moehambouta/Mixed-Signal-PCB/.pages/assets/pcb_3d.gif

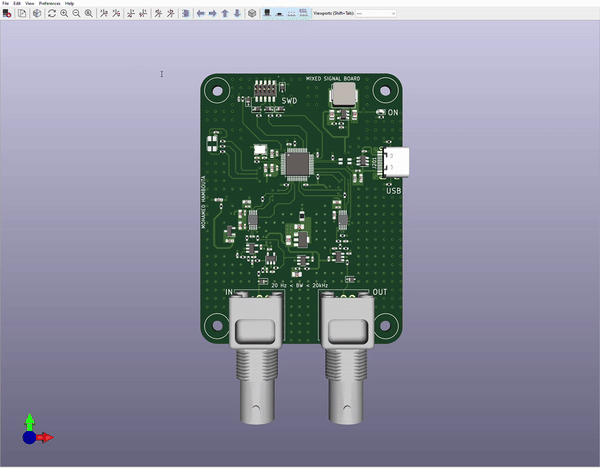
.pages/assets/pcb_3d.gif
