moehambouta/Mixed-Signal-PCB/.pages/assets/adc1.png

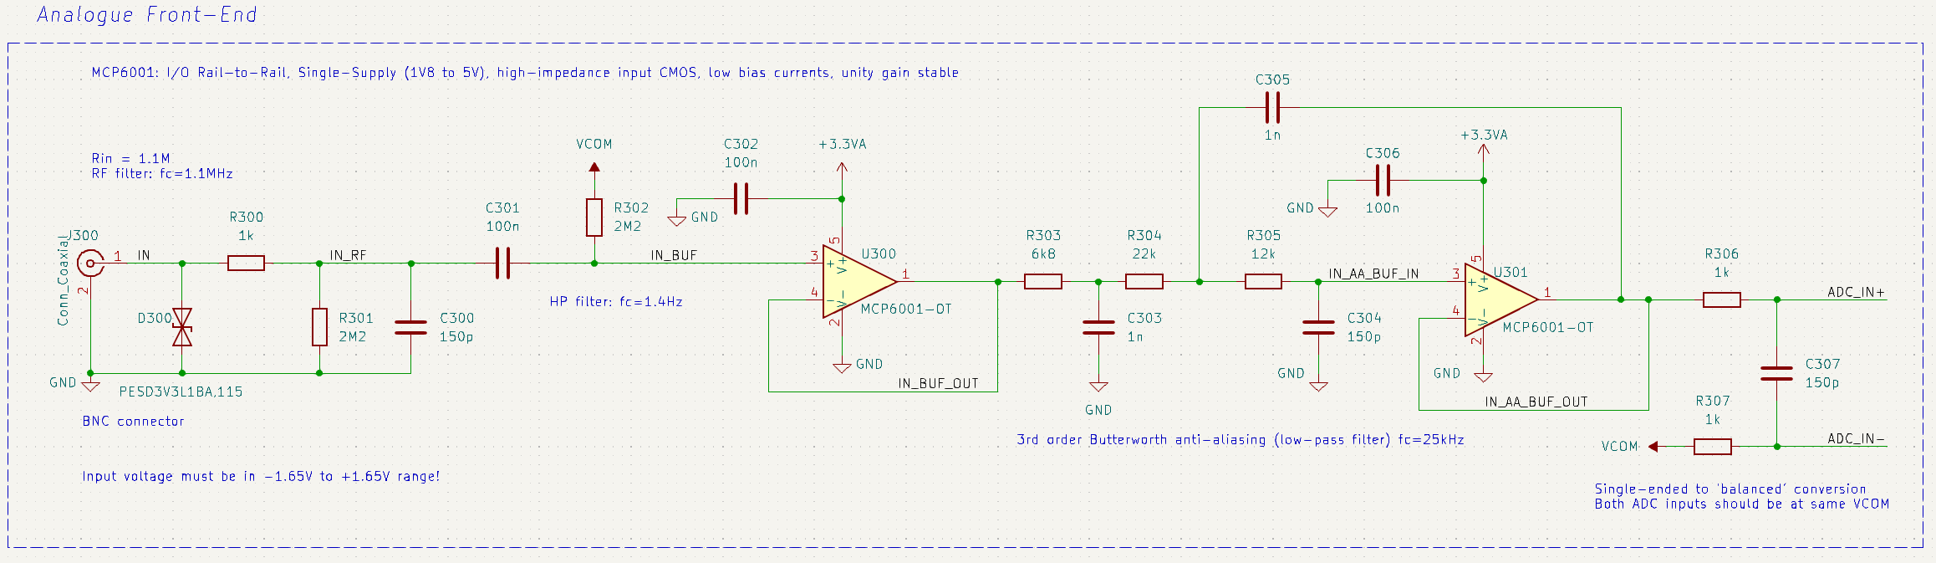
.pages/assets/adc1.png
