moehambouta/Mixed-Signal-PCB/.pages/assets/adc2.png

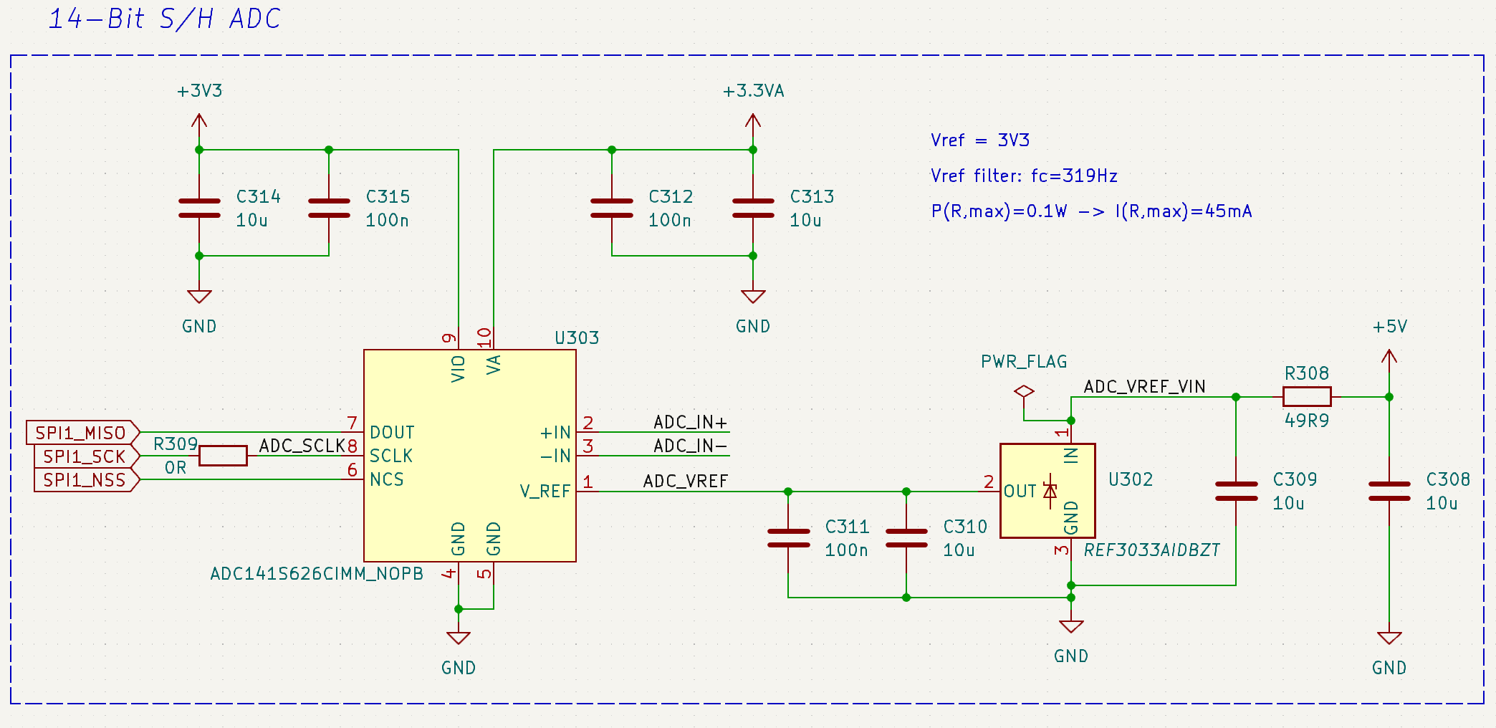
.pages/assets/adc2.png
