moehambouta/Mixed-Signal-PCB/.pages/assets/dac.png

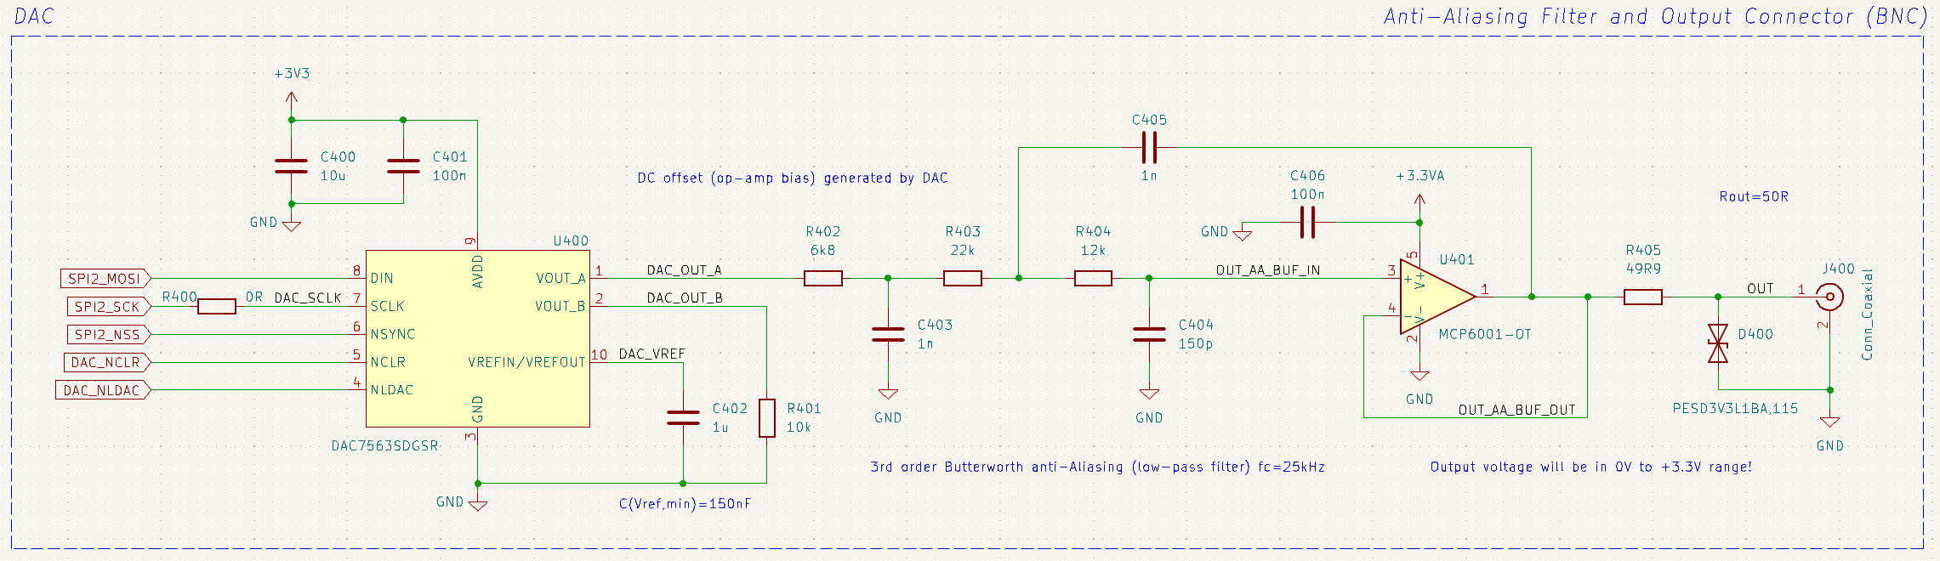
.pages/assets/dac.png
