moehambouta/Mixed-Signal-PCB/.pages/assets/pcb_bcu.png

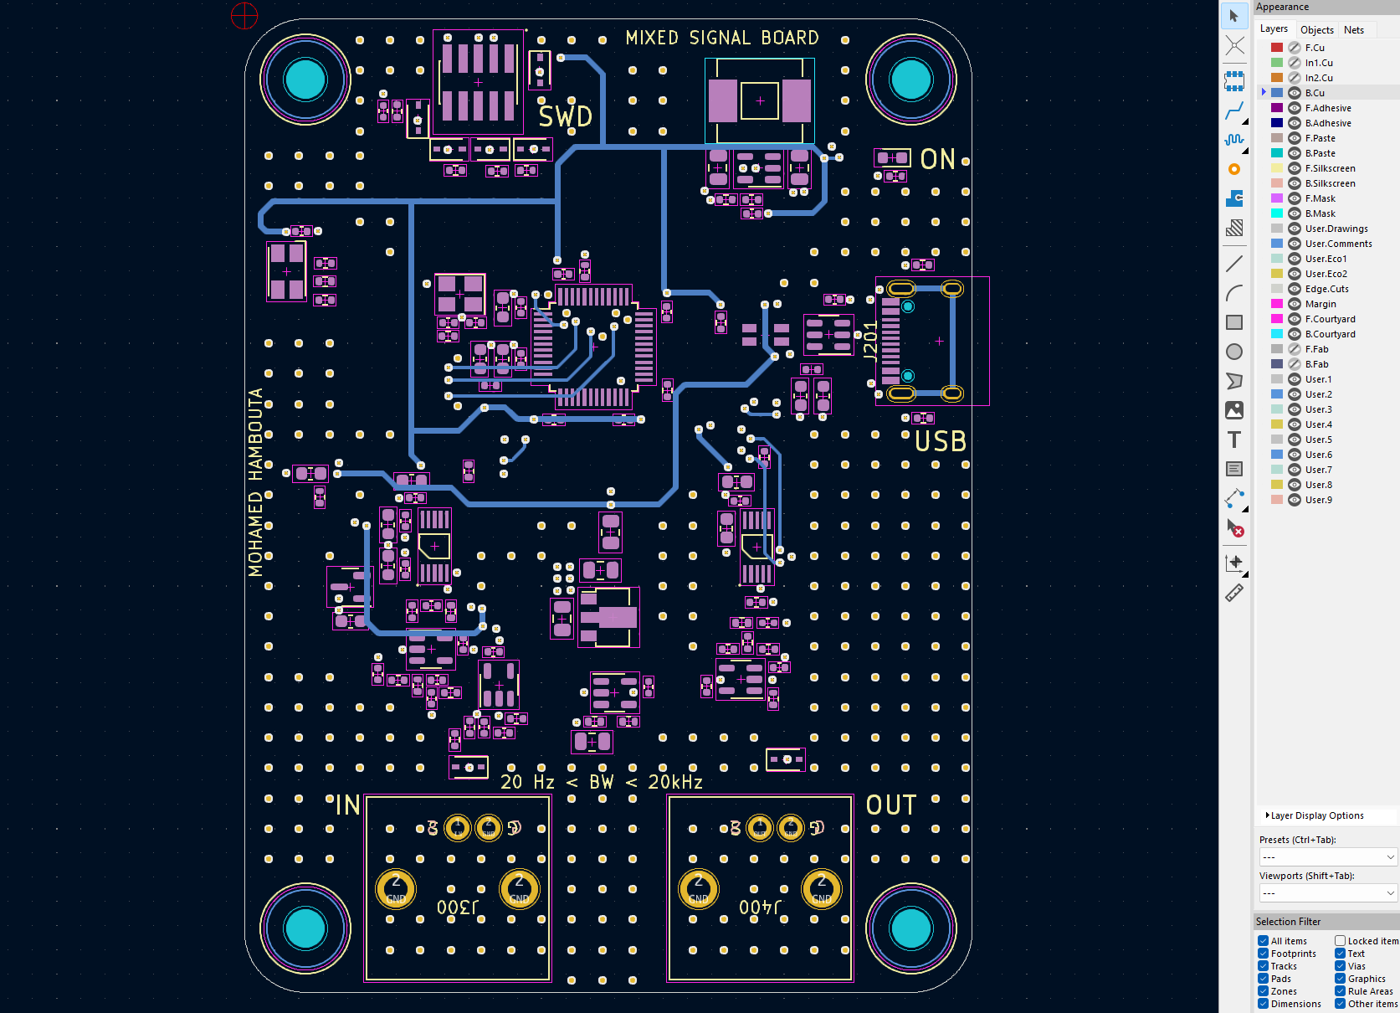
.pages/assets/pcb_bcu.png
