moehambouta/Mixed-Signal-PCB/.pages/assets/pcb_layout.png

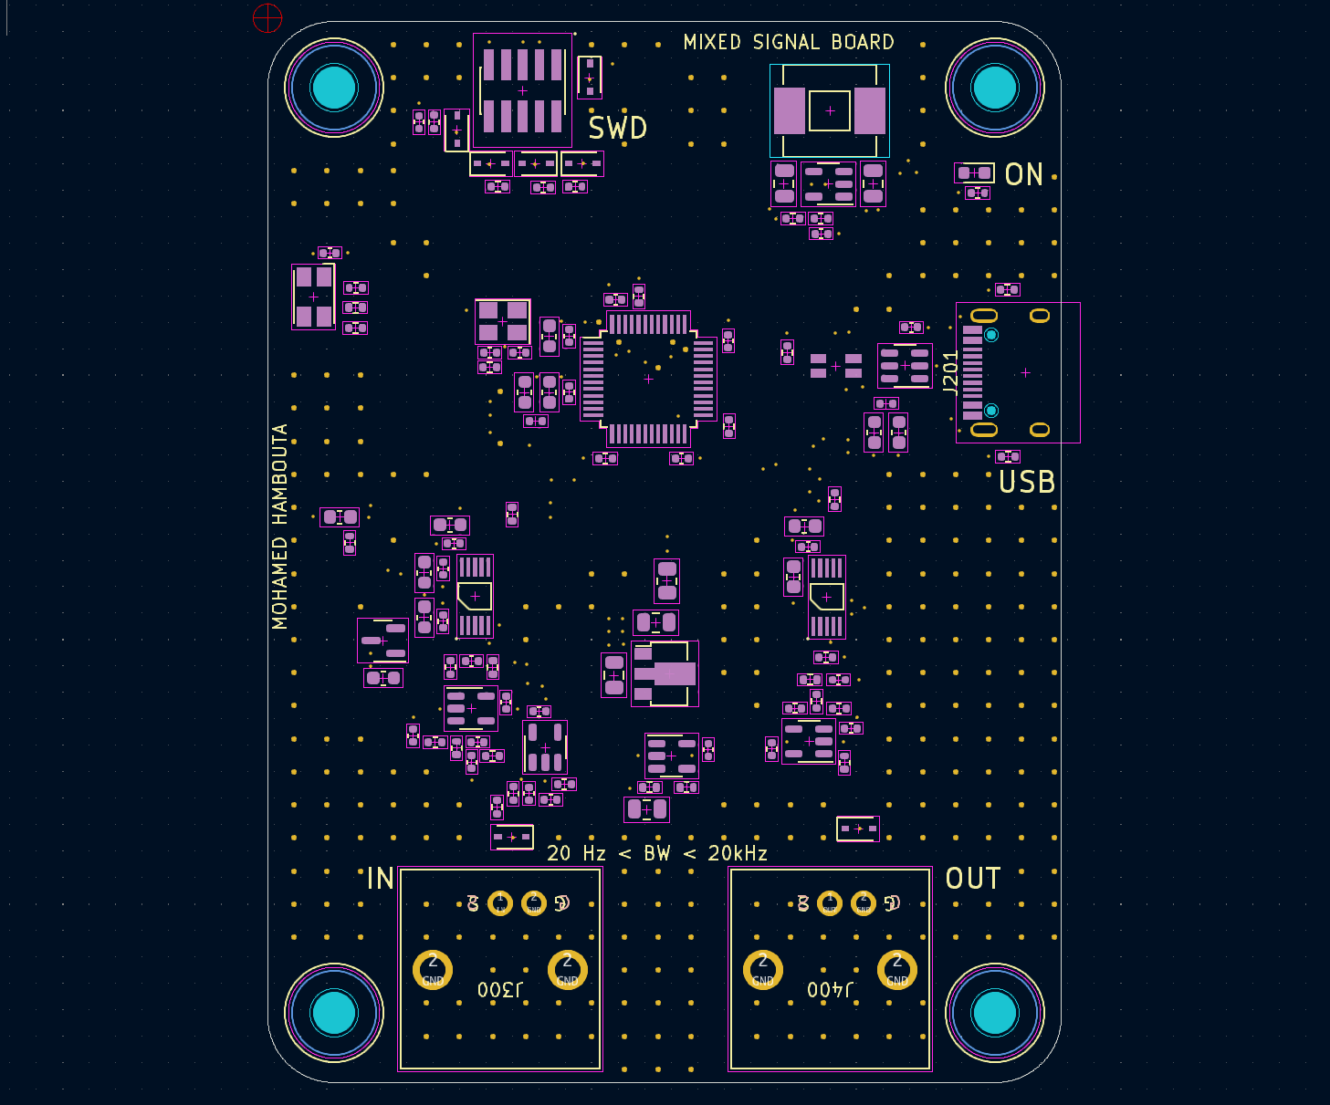
.pages/assets/pcb_layout.png
