moehambouta/Mixed-Signal-PCB/.pages/assets/usb.png

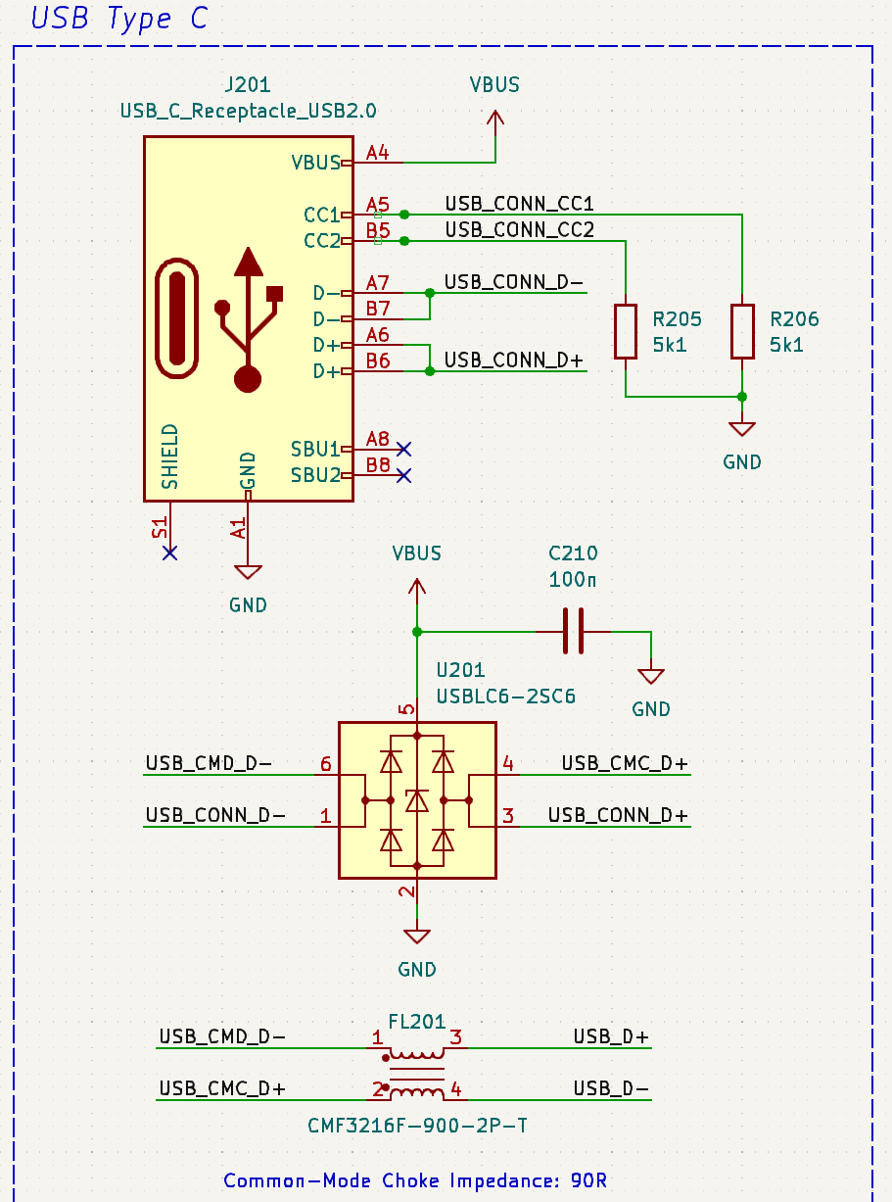
.pages/assets/usb.png
