moehambouta/Mixed-Signal-PCB/Media/adc.png

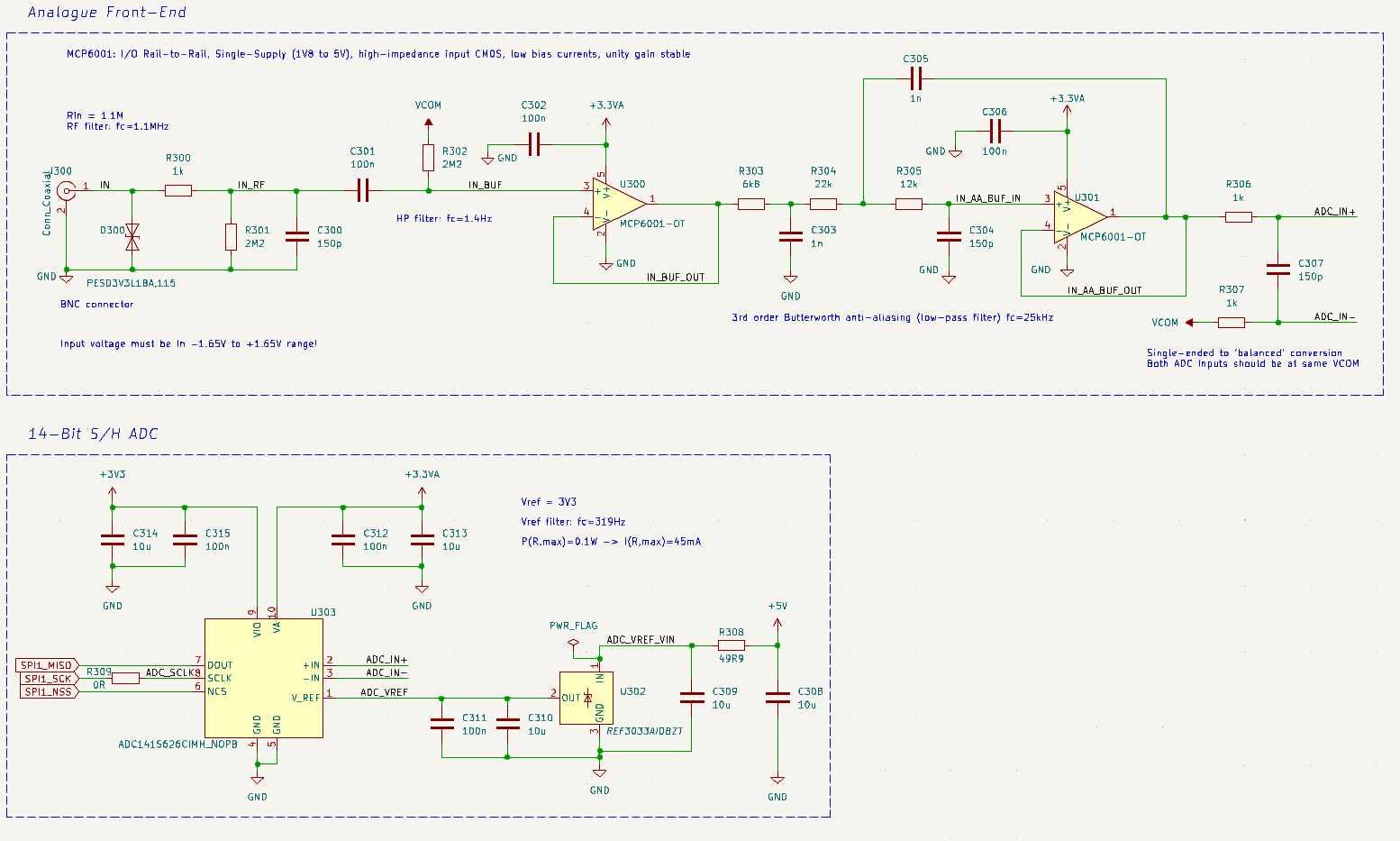
Media/adc.png
