moehambouta/Mixed-Signal-PCB/Media/bc_pcb.png

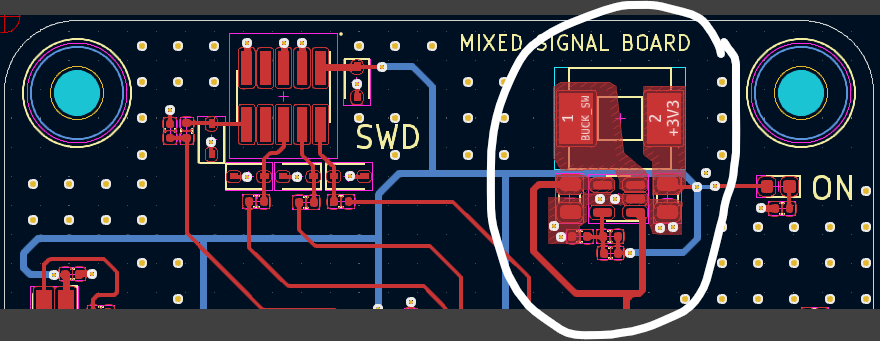
Media/bc_pcb.png
