moehambouta/Mixed-Signal-PCB/Media/bias_gen.png

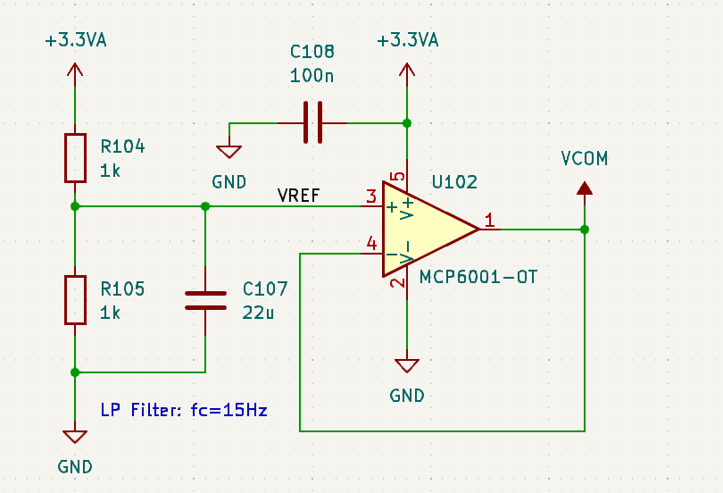
Media/bias_gen.png
