moehambouta/Mixed-Signal-PCB/Media/dac.png

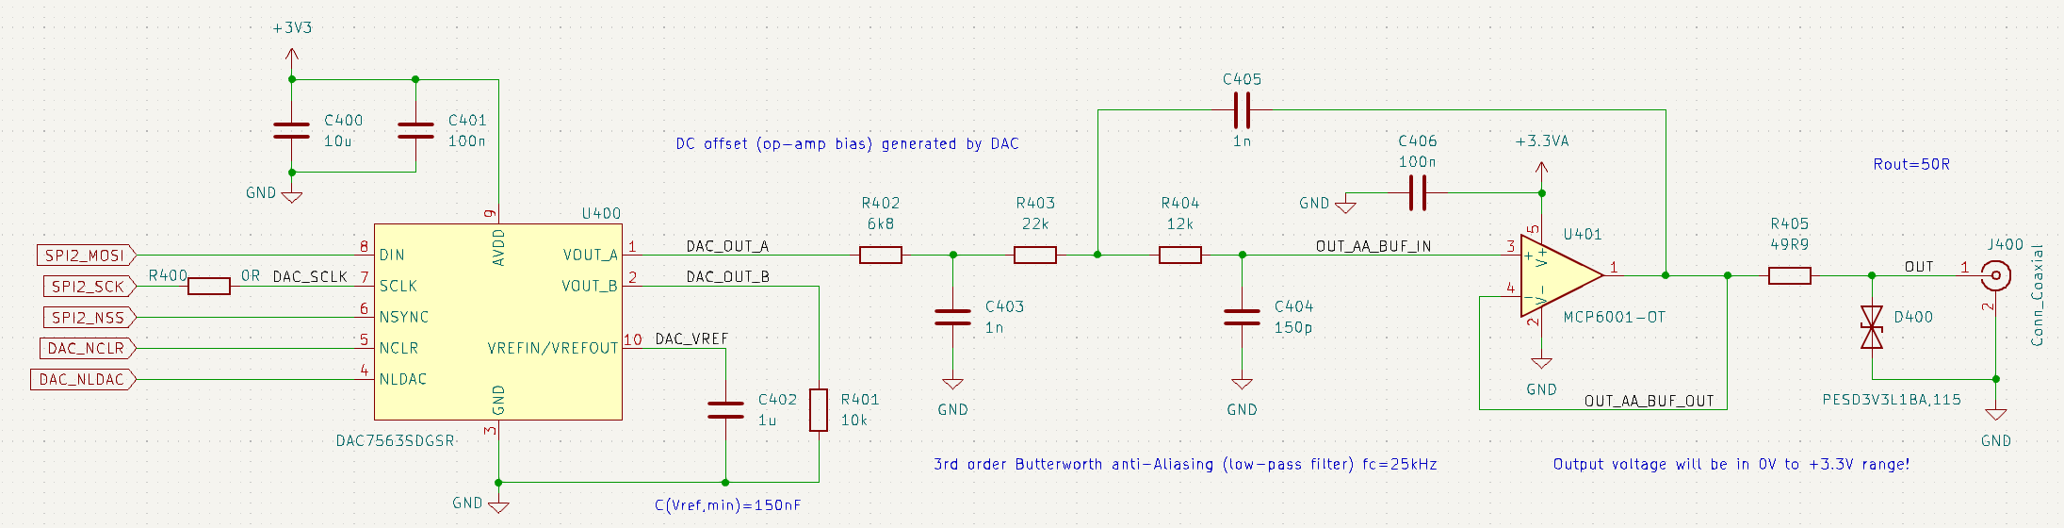
Media/dac.png
