moehambouta/Mixed-Signal-PCB/Media/ldo_pcb.png

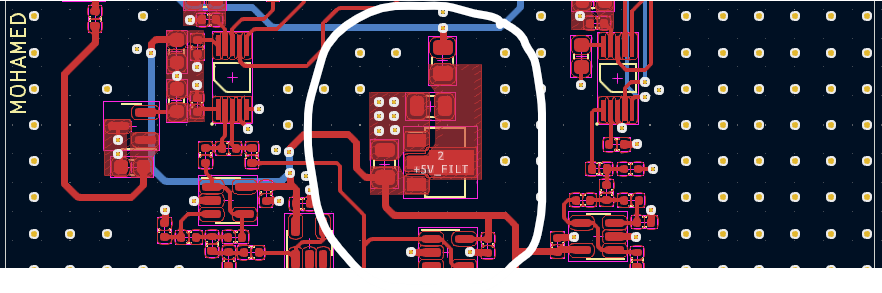
Media/ldo_pcb.png
