moehambouta/Mixed-Signal-PCB/Media/pcb.png

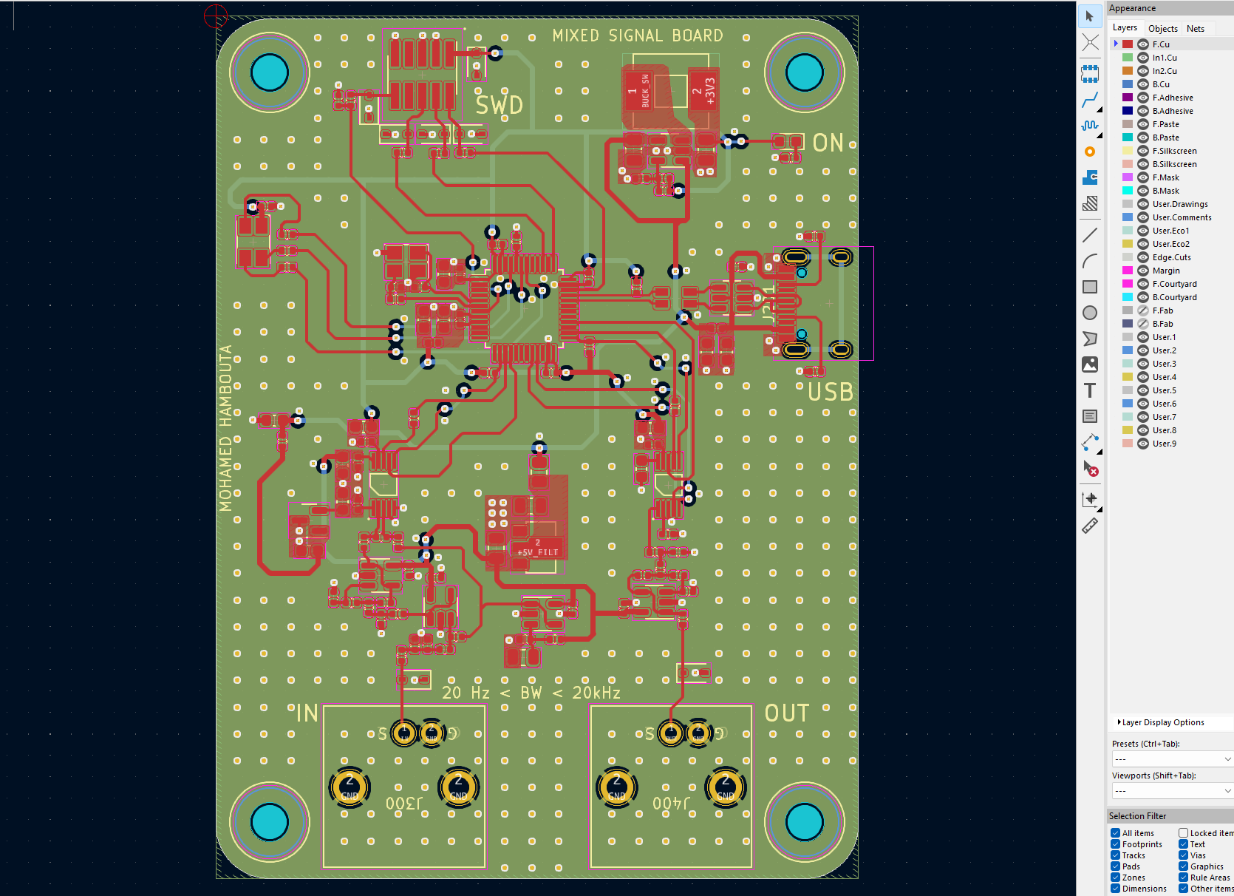
Media/pcb.png
