moehambouta/Mixed-Signal-PCB/Media/pcb_bcu.png

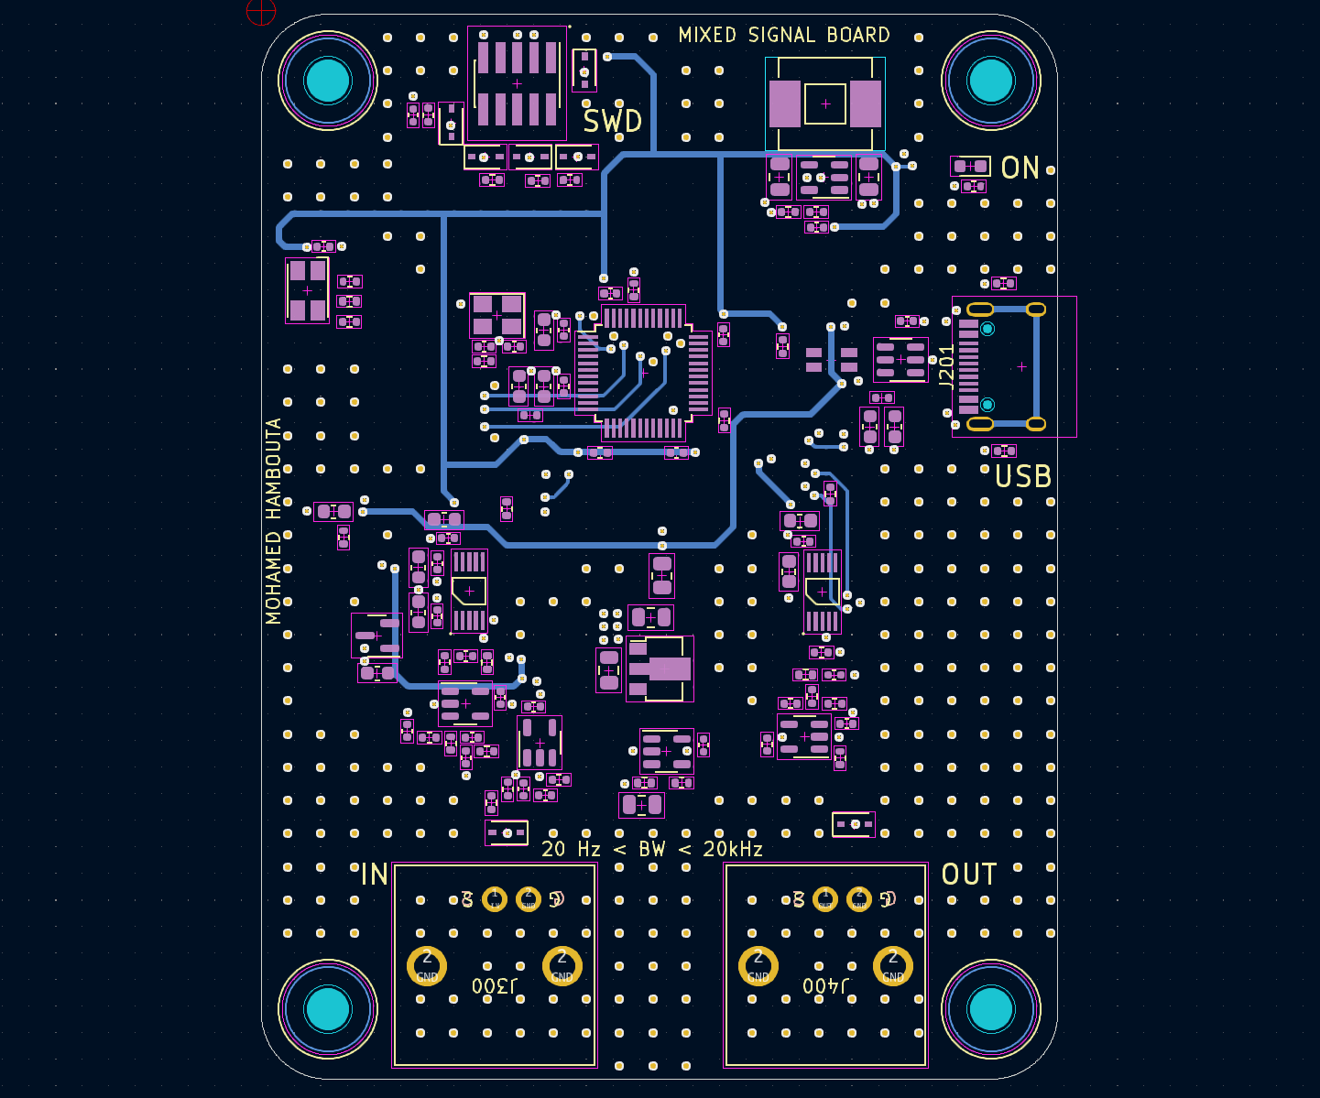
Media/pcb_bcu.png
