moehambouta/Mixed-Signal-PCB/Media/usb.png

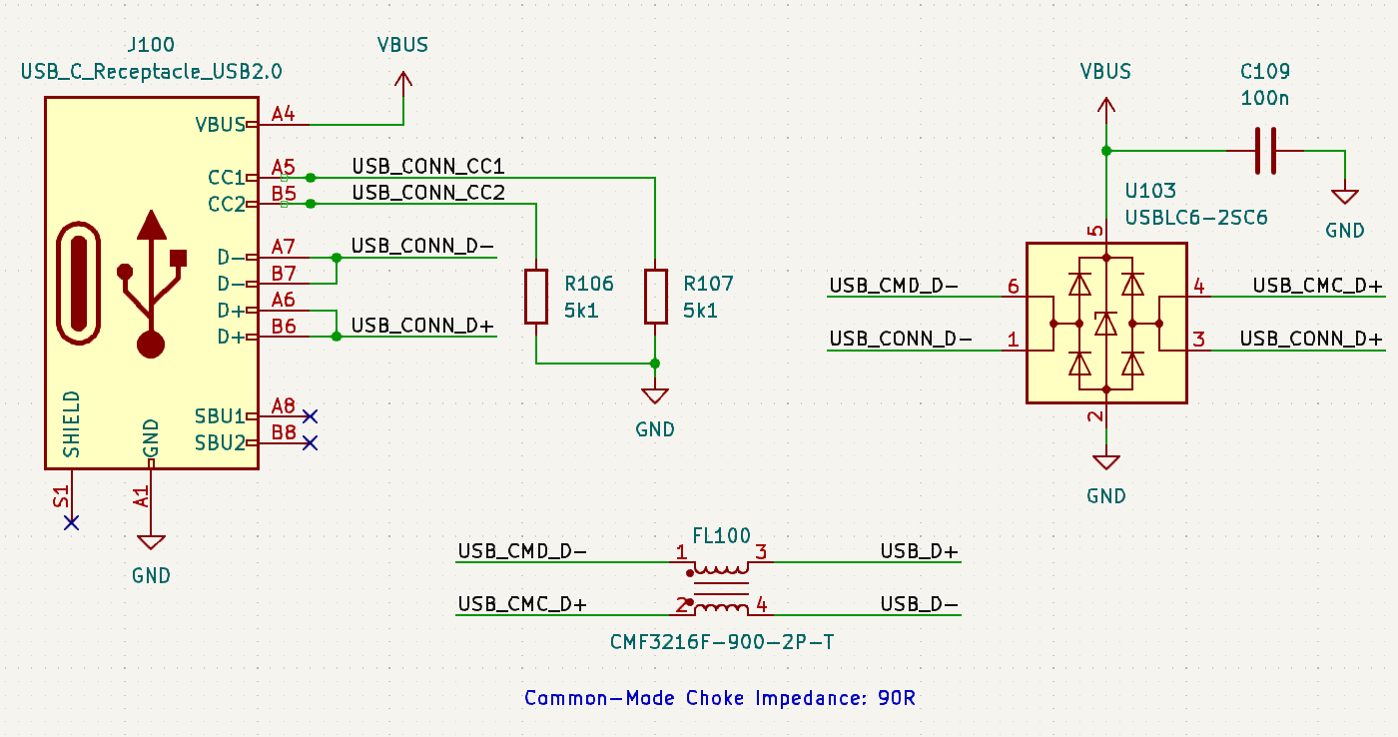
Media/usb.png
